RaduAndre/DeskMixer/firmware/stm32/Core/Inc/sliders.h

/**
 * @file    sliders.h
 * @brief   Analog slider reader for DeskMixer STM32.
 *
 * Reads 5 potentiometer sliders connected to ADC1 channels 0-4
 * (physical pins 10-14 = PA0-PA4).
 *
 * The CubeMX-generated MX_ADC1_Init() only configures a single channel.
 * This driver overrides the channel selection per-read so that all 5
 * channels can be sampled sequentially without needing DMA scan mode.
 * Values are returned in the range 0-1024 (12-bit raw right-shifted by 2,
 * matching the new base-1024 wire protocol).
 */

#ifndef SLIDERS_H
#define SLIDERS_H

#include <stdint.h>

/* ---- Configuration ----------------------------------------------------- */
#define NUM_SLIDERS     5       /**< Number of analog sliders                */
#define SLIDER_MAX_VAL  1024    /**< Volume scale max (base-1024 wire scale) */
#define SLIDER_RAW_MAX  4095    /**< Raw 12-bit ADC maximum value             */

/* ---- Public API -------------------------------------------------------- */

/**
 * @brief  Initialise the slider subsystem.
 *         Must be called after MX_ADC1_Init().
 *         Runs ADC calibration (required on STM32F1 for accuracy).
 */
void SLIDERS_Init(void);

/**
 * @brief  Read all 5 slider values and store internally.
 *         Call this once per main loop iteration.
 */
void SLIDERS_Read(void);

/**
 * @brief  Get the last-read value for a specific slider (0-indexed).
 * @param  index  Slider index [0..NUM_SLIDERS-1]
 * @retval Value in range [0..1024], or 0 on invalid index.
 */
uint16_t SLIDERS_GetValue(uint8_t index);

/**
 * @brief  Pointer to the internal values array for bulk access.
 * @retval Const pointer to array of NUM_SLIDERS uint16_t values.
 */
const uint16_t *SLIDERS_GetAll(void);

/**
 * @brief  Pointer to the raw 12-bit ADC values array [0..4095].
 *         Updated by the last SLIDERS_Read() call.
 * @retval Const pointer to array of NUM_SLIDERS uint16_t values.
 */
const uint16_t *SLIDERS_GetRaw(void);

#endif /* SLIDERS_H */
